N5GEH/n5geh.devices.iot_wa_aio/Firmware/components/AIO/src/AIO_Conf.c

#include "AIO_Conf.h"
#include <string.h>
#include <esp_log.h>

static const char *TAG = "AIO_Conf";

void print_aio_conf(aio_conf_t* conf)
{
	ESP_LOGI(TAG, "AIO configuration:");

	printf("\t%s\n", conf->wifi_ap_ssid);
	printf("\t%s\n", conf->wifi_ap_pass);
	printf("\t%s\n", conf->wifi_sta_ssid);
	printf("\t%s\n", conf->wifi_sta_pass);
	printf("\t%d\n", conf->mqtt_encrypt);
	printf("\t%s\n", conf->mqtt_host);
	printf("\t%d\n", conf->mqtt_port);
	printf("\t%s\n", conf->mqtt_user);
	printf("\t%s\n", conf->mqtt_pass);
	printf("\t%s\n", conf->mqtt_apikey);
	printf("\t%s\n", conf->mqtt_deviceid);
	printf("\t%s\n", conf->mqtt_pub);
	printf("\t%d\n", conf->mqtt_pub_qos);
	printf("\t%s\n", conf->mqtt_sub);
	printf("\t%d\n", conf->mqtt_sub_qos);
	printf("\t%d\n", conf->mqtt_encode);
	printf("\t%d\n", conf->in_mode);
	printf("\t%s\n", conf->in_key);
	printf("\t%f\n", conf->in_min);
	printf("\t%f\n", conf->in_max);
	printf("\t%d\n", conf->in_log_mode);
	printf("\t%f\n", conf->in_log_val);
	printf("\t%d\n", conf->in_rtd);
	printf("\t%d\n", conf->in_wires);
	printf("\t%d\n", conf->out_mode);
	printf("\t%s\n", conf->out_key);
	printf("\t%f\n", conf->out_min);
	printf("\t%f\n", conf->out_max);
}

aio_conf_field_t next_field(char* str, uint16_t length, uint16_t offset)
{
	aio_conf_field_t aio_conf_field;
	memset(&aio_conf_field, 0, sizeof(aio_conf_field_t));

	for (int i = offset; i <= length; i++)
		if ((str[i] == '\r') || (i == length))
			for (int j = offset; j < i; j++)
				if (str[j] == '=') {
					memcpy(aio_conf_field.name, &str[offset], j - offset);
					aio_conf_field.name[j - offset] = '\0';
					memcpy(aio_conf_field.value, &str[j + 1], i - j - 1);
					aio_conf_field.value[i - j - 1] = '\0';
					aio_conf_field.offset = i + 2;
					return aio_conf_field;
				}

	return aio_conf_field;
}

esp_err_t write_aio_conf(aio_conf_t* conf)
{
	ESP_LOGI(TAG, "Write AIO configuration to NVS");
	nvs_handle my_handle;
	esp_err_t err;

	// Open
	err = nvs_open(STORAGE_NAMESPACE, NVS_READWRITE, &my_handle);
	if (err != ESP_OK)
		return err;

	// Write value including previously saved blob if available
	size_t required_size = sizeof(aio_conf_t) + sizeof(uint32_t);
	err = nvs_set_blob(my_handle, "aio_conf", conf, required_size);

	if (err != ESP_OK)
		return err;

	// Commit
	err = nvs_commit(my_handle);
	if (err != ESP_OK)
		return err;

	// Close
	nvs_close(my_handle);
	return ESP_OK;
}

/*	Exports the configuration
	inside an HTML form provided
	as a regular expression.
 */
esp_err_t export_aio_conf(aio_conf_t* conf, char* str, const char* reg_str)
{
	int ret = sprintf(str, reg_str,
		(conf->wifi_ap_ssid[0] != '\0') ? (conf->wifi_ap_ssid) : "\0",
		(conf->wifi_ap_pass[0] != '\0') ? (conf->wifi_ap_pass) : "\0",
		(conf->wifi_sta_ssid[0] != '\0') ? (conf->wifi_sta_ssid) : "\0",
		(conf->wifi_sta_pass[0] != '\0') ? (conf->wifi_sta_pass) : "\0",
		(conf->mqtt_encrypt == 0) ? "selected" : "\0",
		(conf->mqtt_encrypt == 1) ? "selected" : "\0",
		(conf->mqtt_host[0] != '\0') ? (conf->mqtt_host) : "\0",
		conf->mqtt_port,
		(conf->mqtt_user[0] != '\0') ? (conf->mqtt_user) : "\0",
		(conf->mqtt_pass[0] != '\0') ? (conf->mqtt_pass) : "\0",
		(conf->mqtt_apikey[0] != '\0') ? (conf->mqtt_apikey) : "\0",
		(conf->mqtt_deviceid[0] != '\0') ? (conf->mqtt_deviceid) : "\0",
		(conf->mqtt_pub[0] != '\0') ? (conf->mqtt_pub) : "\0",
		(conf->mqtt_pub_qos == 0) ? "selected" : "\0",
		(conf->mqtt_pub_qos == 1) ? "selected" : "\0",
		(conf->mqtt_pub_qos == 2) ? "selected" : "\0",
		(conf->mqtt_sub[0] != '\0') ? (conf->mqtt_sub) : "\0",
		(conf->mqtt_sub_qos == 0) ? "selected" : "\0",
		(conf->mqtt_sub_qos == 1) ? "selected" : "\0",
		(conf->mqtt_sub_qos == 2) ? "selected" : "\0",
		(conf->mqtt_encode == 0) ? "selected" : "\0",
		(conf->mqtt_encode == 1) ? "selected" : "\0",
		(conf->in_mode == 0) ? "selected" : "\0",
		(conf->in_mode == 1) ? "selected" : "\0",
		(conf->in_mode == 2) ? "selected" : "\0",
		(conf->in_mode == 3) ? "selected" : "\0",
		(conf->in_mode == 4) ? "selected" : "\0",
		(conf->in_mode == 5) ? "selected" : "\0",
		(conf->in_key[0] != '\0') ? (conf->in_key) : "\0",
		conf->in_min,
		conf->in_max,
		(conf->in_log_mode == 0) ? "selected" : "\0",
		(conf->in_log_mode == 1) ? "selected" : "\0",
		conf->in_log_val,
		(conf->in_rtd == 0) ? "selected" : "\0",
		(conf->in_rtd == 1) ? "selected" : "\0",
		(conf->in_wires == 0) ? "selected" : "\0",
		(conf->in_wires == 1) ? "selected" : "\0",
		(conf->in_wires == 2) ? "selected" : "\0",
		(conf->out_mode == 0) ? "selected" : "\0",
		(conf->out_mode == 1) ? "selected" : "\0",
		(conf->out_mode == 2) ? "selected" : "\0",
		(conf->out_mode == 3) ? "selected" : "\0",
		(conf->out_mode == 4) ? "selected" : "\0",
		(conf->out_key[0] != '\0') ? (conf->out_key) : "\0",
		conf->out_min,
		conf->out_max);

	if (ret < 0)
		return ESP_ERR_NOT_FOUND;
	return ESP_OK;
}

/*	Imports the configuration from
	a string in standard HTML form format.
 */
esp_err_t import_aio_conf(aio_conf_t* conf, char* str)
{
	ESP_LOGI(TAG, "Importing AIO configuration");

	int len = strlen(str);
	int field_num = 0;

	// Check number of fields
	for (int i = 0; i < len; i++)
		if (str[i] == '=')
			//printf("%02x", str[i]);
			field_num++;

	if (field_num < 28)
		return ESP_FAIL;

	aio_conf_field_t field;

	// SSID_AP
	field = next_field(str, len, 0);
	memcpy(conf->wifi_ap_ssid, field.value, 32);

	// PASS_AP
	field = next_field(str, len, field.offset);
	memcpy(conf->wifi_ap_pass, field.value, 64);

	// SSID_STA
	field = next_field(str, len, field.offset);
	memcpy(conf->wifi_sta_ssid, field.value, 32);

	// PASS_STA
	field = next_field(str, len, field.offset);
	memcpy(conf->wifi_sta_pass, field.value, 64);

	// ENCRYPTION
	field = next_field(str, len, field.offset);
	conf->mqtt_encrypt = atoi(field.value);

	// HOST
	field = next_field(str, len, field.offset);
	memcpy(conf->mqtt_host, field.value, 32);

	// PORT
	field = next_field(str, len, field.offset);
	conf->mqtt_port = atoi(field.value);

	// USERNAME
	field = next_field(str, len, field.offset);
	memcpy(conf->mqtt_user, field.value, 32);

	// PASSWORD
	field = next_field(str, len, field.offset);
	memcpy(conf->mqtt_pass, field.value, 32);

	// APIKEY
	field = next_field(str, len, field.offset);
	memcpy(conf->mqtt_apikey, field.value, 32);

	// DEVICEID
	field = next_field(str, len, field.offset);
	memcpy(conf->mqtt_deviceid, field.value, 32);

	// PUB_TOPIC
	field = next_field(str, len, field.offset);
	memcpy(conf->mqtt_pub, field.value, 72);

	// PUB_QOS
	field = next_field(str, len, field.offset);
	conf->mqtt_pub_qos = atoi(field.value);

	// SUB_TOPIC
	field = next_field(str, len, field.offset);
	memcpy(conf->mqtt_sub, field.value, 72);

	// SUB_QOS
	field = next_field(str, len, field.offset);
	conf->mqtt_sub_qos = atoi(field.value);

	// ENCODE
	field = next_field(str, len, field.offset);
	conf->mqtt_encode = atoi(field.value);

	// IN_MODE
	field = next_field(str, len, field.offset);
	conf->in_mode = atoi(field.value);

	// IN_KEY
	field = next_field(str, len, field.offset);
	memcpy(conf->in_key, field.value, 16);

	// IN_MIN
	field = next_field(str, len, field.offset);
	conf->in_min = atof(field.value);

	// IN_MAX
	field = next_field(str, len, field.offset);
	conf->in_max = atof(field.value);

	// IN_LOG_MODE
	field = next_field(str, len, field.offset);
	conf->in_log_mode = atoi(field.value);

	// IN_LOG_VALUE
	field = next_field(str, len, field.offset);
	conf->in_log_val = atof(field.value);

	// IN_RTD_NOMINAL
	field = next_field(str, len, field.offset);
	conf->in_rtd = atoi(field.value);

	// IN_RTD_WIRES
	field = next_field(str, len, field.offset);
	conf->in_wires = atoi(field.value);

	// OUT_MODE
	field = next_field(str, len, field.offset);
	conf->out_mode = atoi(field.value);

	// OUT_KEY
	field = next_field(str, len, field.offset);
	memcpy(conf->out_key, field.value, 16);

	// OUT_MIN
	field = next_field(str, len, field.offset);
	conf->out_min = atof(field.value);

	// OUT_MAX
	field = next_field(str, len, field.offset);
	conf->out_max = atof(field.value);
	
	return ESP_OK;
}

/* Read from NVS and print restart counter
   and the table with run times.
   Return an error if anything goes wrong
   during this process.
 */
esp_err_t init_CONF(aio_conf_t* aio_conf, aio_conf_init_t _init)
{
	ESP_LOGI(TAG, "Init NVS Memory module");

	ESP_ERROR_CHECK(nvs_flash_init());			// Init flash memory

	nvs_handle my_handle;
	
	// Open
	ESP_ERROR_CHECK(nvs_open(STORAGE_NAMESPACE, NVS_READWRITE, &my_handle));

	switch(_init) {
		case AIO_CONF_INIT_DEFAULT:
			ESP_LOGI(TAG, "NVS configuration override: using default");
			*aio_conf = aio_conf_default;
			write_aio_conf(aio_conf);
			nvs_close(my_handle);
		break;

		case AIO_CONF_INIT_CUSTOM:
			ESP_LOGI(TAG, "NVS configuration override: using custom");
			*aio_conf = aio_conf_custom;
			write_aio_conf(aio_conf);
			nvs_close(my_handle);
		break;

		case AIO_CONF_INIT_MEMORY:
		{
			// Read run time blob
			size_t required_size = 0;  // value will default to 0, if not set yet in NVS

			// obtain required memory space to store blob being read from NVS
			esp_err_t err;
			err = nvs_get_blob(my_handle, "aio_conf", NULL, &required_size);
			if (err != ESP_OK && err != ESP_ERR_NVS_NOT_FOUND)
				return err;

			if (required_size == 0) {
				ESP_LOGW(TAG, "NVS configuration not found: using default");
				*aio_conf = aio_conf_default;
				write_aio_conf(aio_conf);
				nvs_close(my_handle);
			}
			else {
				ESP_LOGI(TAG, "NVS configuration found: using memory");
				err = nvs_get_blob(my_handle, "aio_conf", aio_conf, &required_size);
				if (err != ESP_OK) {
					ESP_LOGE(TAG, "Memory reading error");
					nvs_close(my_handle);
					init_CONF(aio_conf, AIO_CONF_INIT_DEFAULT);
				}
			}
		}
		break;
	}
	
	return ESP_OK;
}
